drjaydenm/macropod/code/src/main.h

#ifndef __MAIN_H
#define __MAIN_H

#include <stdint.h>

#ifdef MCU_CLASS_F0
    #include "stm32f0xx.h"
    #include "stm32f0xx_hal.h"
#elif MCU_CLASS_L0
    #include "stm32l0xx.h"
    #include "stm32l0xx_hal.h"
#endif

#include "gpio_pin.h"
#include "keyboard.h"

#define FLASH_MILLIS 2
#define PAUSE_MILLIS 2500

void SetupGPIO();
void SystemClockConfig(void);

#endif
